dchwebb/Sinosaur/Sinosaur/src/initialisation.h

#pragma once

#include "stm32g4xx.h"
#include "GpioPin.h"
#include <algorithm>
#include <Array>

extern volatile uint32_t SysTickVal;


struct ADCValues {
	uint16_t Sine3_Rate;		// PC2	ADC12_IN8	1

	uint16_t Sine2_Rate;		// PE11	ADC345_IN15	3
	uint16_t Sine1_Level;		// PE9	ADC3_IN2	3
	uint16_t Sine2_Level;		// PE10	ADC345_IN14	3
	uint16_t Sine3_Level;		// PE7	ADC3_IN4,	3

	uint16_t Sine1_Rate;		// PE8	ADC345_IN6	4
	uint16_t Swell_Rate;		// PD9	ADC4_IN13	4
	uint16_t Swell_Level;		// PE12	ADC345_IN16	4
	uint16_t Ramp_Rate;			// PE14	ADC4_IN1	4
	uint16_t Ramp_Level;		// PE15	ADC4_IN2	4
};



extern volatile ADCValues adc;
extern GpioPin debugPin1;
extern GpioPin debugPin2;

#define sysTickInterval 1000						// 1ms
static constexpr uint32_t SampleRate =  40000;

static constexpr float pi = std::numbers::pi_v<float>;
static constexpr float pi_x_2 = pi * 2.0f;
static constexpr float reciprocal4096 = 1.0f / 4095.0f;

void InitClocks();
void InitHardware();
void InitSysTick();
void InitDAC();
void InitADC1(volatile uint16_t* buffer, uint16_t channels);
void InitADC3(volatile uint16_t* buffer, uint16_t channels);
void InitADC4(volatile uint16_t* buffer, uint16_t channels);
void InitCordic();
void InitPWMTimer();
void InitOutputTimer();
